tljk/youdao_wordbook/Spider_JS_ReverseParsin/images/1.jpg

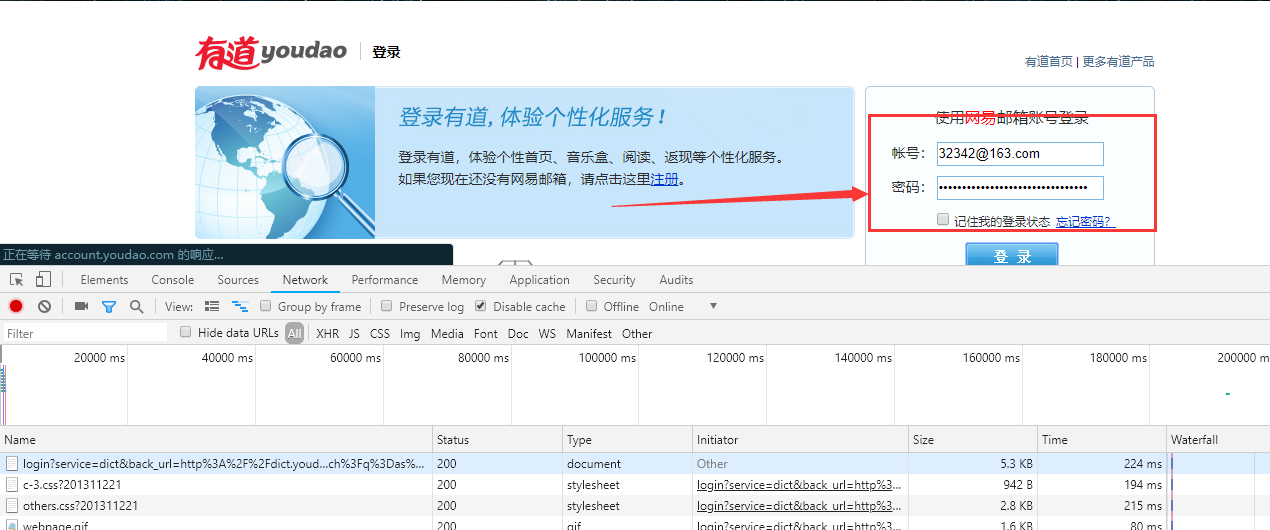
Spider_JS_ReverseParsin/images/1.jpg
