tljk/youdao_wordbook/Spider_JS_ReverseParsin/images/2.png

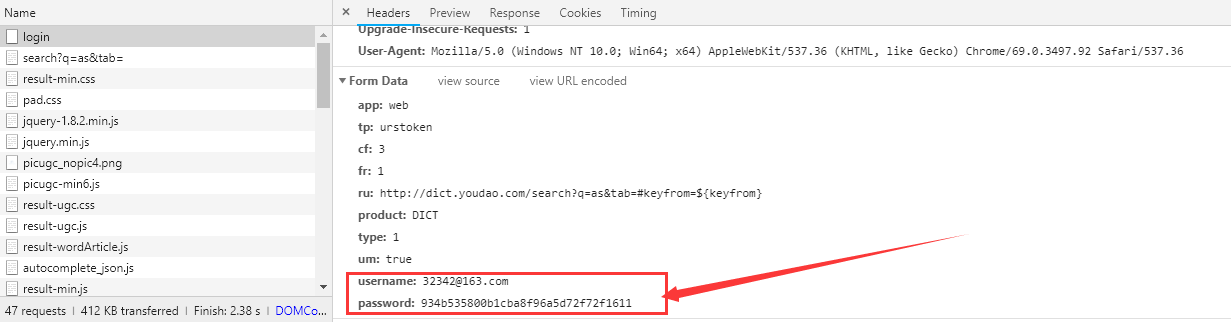
Spider_JS_ReverseParsin/images/2.png
