tljk/youdao_wordbook/Spider_JS_ReverseParsin/images/20181111225620.png

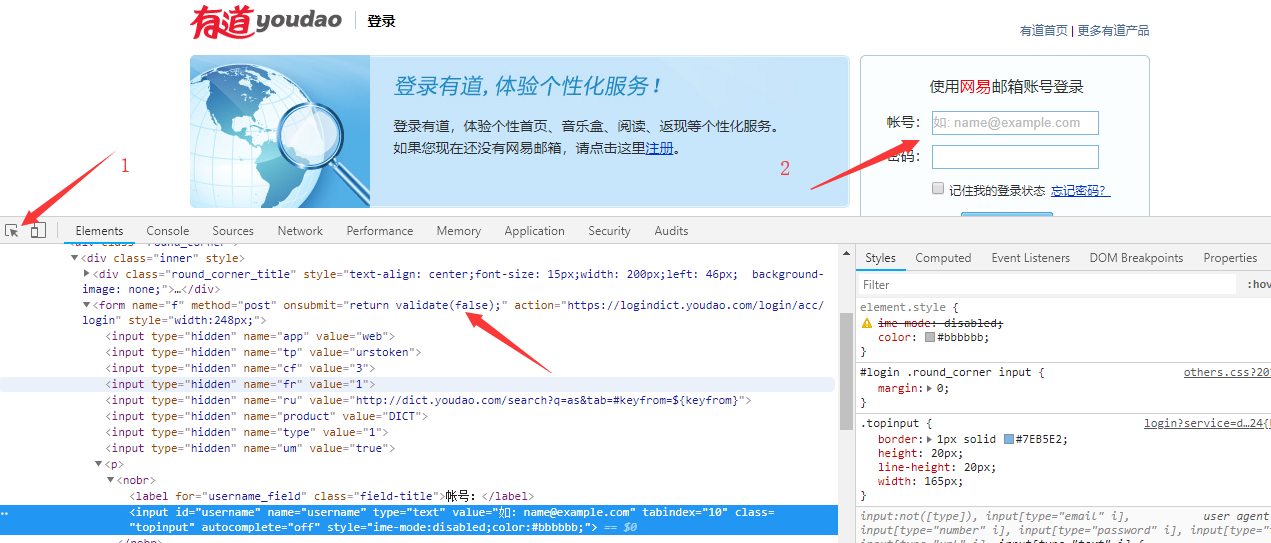
Spider_JS_ReverseParsin/images/20181111225620.png
