tljk/youdao_wordbook/Spider_JS_ReverseParsin/images/QQ截图20181111225947.jpg

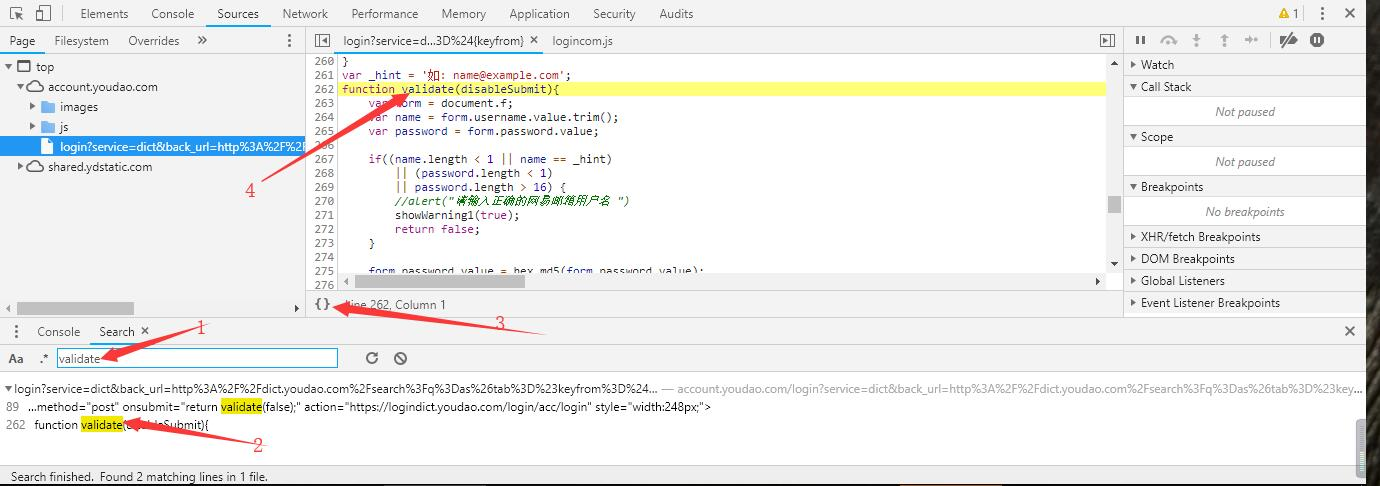
Spider_JS_ReverseParsin/images/QQ截图20181111225947.jpg
