tljk/youdao_wordbook/Spider_JS_ReverseParsin/images/QQ截图20181111230943.jpg

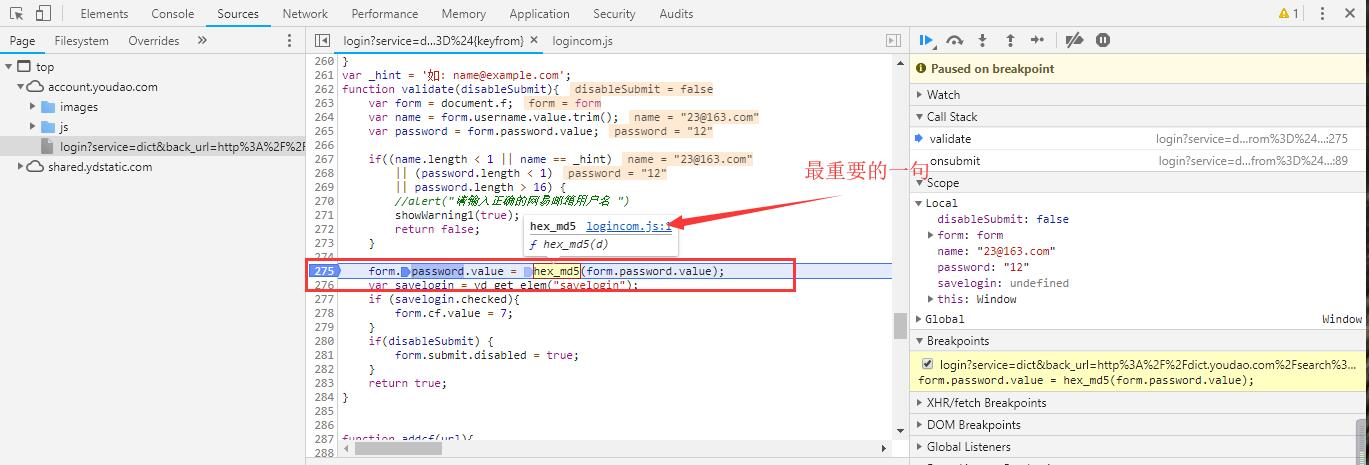
Spider_JS_ReverseParsin/images/QQ截图20181111230943.jpg
